swift502/KrtkusRetro/images/5.webp

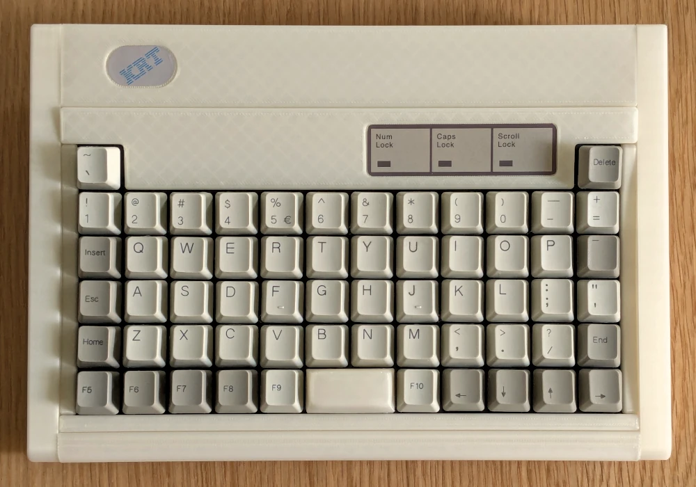
images/5.webp
